louismessonnier/anki-macropad/images/how-keycaps-are-measured.webp

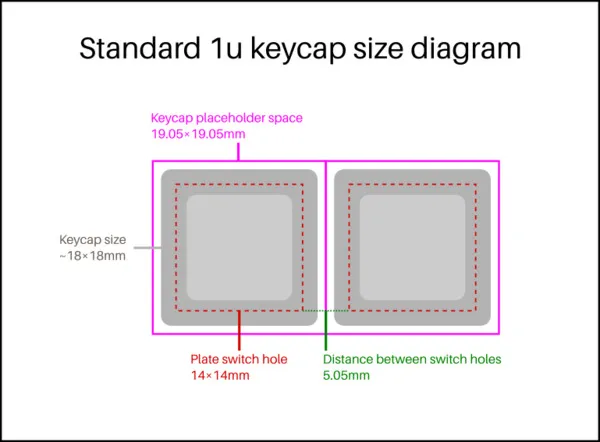
images/how-keycaps-are-measured.webp
